RobertGawron/SemiconductorRadioactivityDetector/Software/HardwareDataLogger/Software/NUCLEO-F091RC/Inc/gm_display_labels.h

#ifndef GMDISPLAY_LABELS_H_
#define GMDISPLAY_LABELS_H_

const char* labelMinuteCounter;
const char* labeWelcomeTop;
const char* labeWelcomeBottom;
const char* labelError;
const char* labelDosageUnit;
#endif
