RobertGawron/SemiconductorRadioactivityDetector/Software/HardwareDataLogger/Software/NUCLEO-F091RC/Inc/gm_measurement_calculator.h

#ifndef GMMEASUREMENTCALCULATOR_H_
#define GMMEASUREMENTCALCULATOR_H_

void GMMeasurementCalculator_Init();

void GMMeasurementCalculator_OnSamplingDone();

void GMMeasurementCalculator_OnGMPulseObserved();

#endif
