RobertGawron/SemiconductorRadioactivityDetector/Software/HardwareDataLogger/Software/NUCLEO-F091RC/Src/gm_display_labels.c

#include "gm_display_labels.h"

const char* labelMinuteCounter = "cpm";
const char* labeWelcomeTop = "collecting sample";
const char* labeWelcomeBottom = "please wait 60sec.";
const char* labelError = "## error ##";
// TODO label value
const char* labelDosageUnit = "";
